ShoMisawa/90-800_Tester/Firmware/90800_Tester_u8g2_V4_3/graphics.h

#ifndef _GRAPHICS_H
#define _GRAPHICS_H



// images from https://lopaka.app/
static const unsigned char image_Voltage_16x16_bits[] U8X8_PROGMEM = {0x00,0x00,0x00,0x00,0x00,0x02,0x00,0x03,0x80,0x01,0xc0,0x01,0xe0,0x00,0xf0,0x07,0x80,0x03,0xc0,0x01,0xc0,0x00,0x60,0x00,0x20,0x00,0x00,0x00,0x00,0x00,0x00,0x00};
static const unsigned char image_icons8_outline_effect_tickmark_under_a_square_box_24_bits[] U8X8_PROGMEM = {0xfe,0xff,0x7f,0xff,0xff,0xff,0xff,0xff,0xff,0xff,0xff,0xff,0xff,0xff,0xff,0xff,0xff,0xf8,0xff,0x7f,0xf0,0xff,0x3f,0xf0,0xff,0x1f,0xf0,0xff,0x1f,0xf8,0xff,0x0f,0xfc,0x1f,0x07,0xfe,0x0f,0x02,0xff,0x0f,0x00,0xff,0x0f,0x80,0xff,0x1f,0xc0,0xff,0x7f,0xe0,0xff,0xff,0xf0,0xff,0xff,0xf1,0xff,0xff,0xff,0xff,0xff,0xff,0xff,0xff,0xff,0xff,0xff,0xff,0xff,0xfe,0xff,0x7f};
static const unsigned char image_icons8_switch_24__1__bits[] U8X8_PROGMEM = {0x00,0x00,0x00,0x00,0x00,0x00,0x00,0x00,0x00,0x00,0x00,0x00,0x00,0x00,0x00,0x00,0x00,0x00,0xe0,0xff,0x07,0xf8,0xff,0x1f,0x1c,0x00,0x38,0x0c,0x80,0x37,0x06,0xc0,0x6f,0x06,0xc0,0x6f,0x06,0xc0,0x6f,0x06,0xc0,0x6f,0x0c,0x80,0x37,0x1c,0x00,0x38,0xf8,0xff,0x1f,0xe0,0xff,0x07,0x00,0x00,0x00,0x00,0x00,0x00,0x00,0x00,0x00,0x00,0x00,0x00,0x00,0x00,0x00,0x00,0x00,0x00};
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
  reset_bitmap__a_frm18_40,
  reset_bitmap__a_frm19_40,
  reset_bitmap__a_frm20_50,
  reset_bitmap__a_frm21_40,
  reset_bitmap__a_frm22_40,
  reset_bitmap__a_frm23_40,
  reset_bitmap__a_frm24_40,
  reset_bitmap__a_frm25_40,
  reset_bitmap__a_frm26_50,
  reset_bitmap__a_frm27_50,
  
};

#endif
